Malavegeetanjali0481/HexaGLAM_K/App/App_QR.png

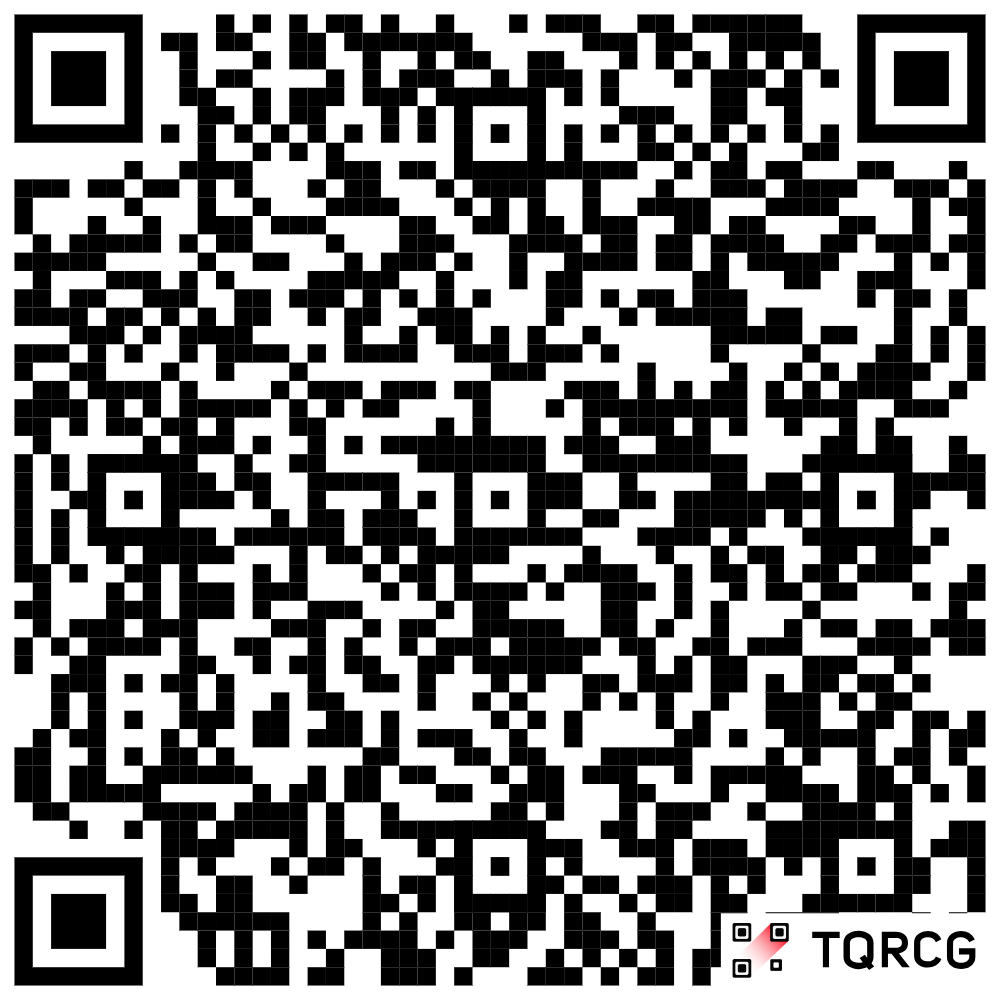
App/App_QR.png
