Malavegeetanjali0481/HexaGLAM_K/Brouchure/hexa video qr canva.png

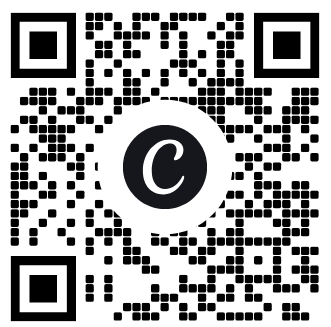
Brouchure/hexa video qr canva.png
